awm/rvfs-testbed/experiments/seven_segment/seven_segment.kicad_pcb

## KiCad design Diagramas_y_Bocetos/Diagrama_kicad/Cascarrabias_Kicad/Cascarrabias_Kicad.kicad_sch

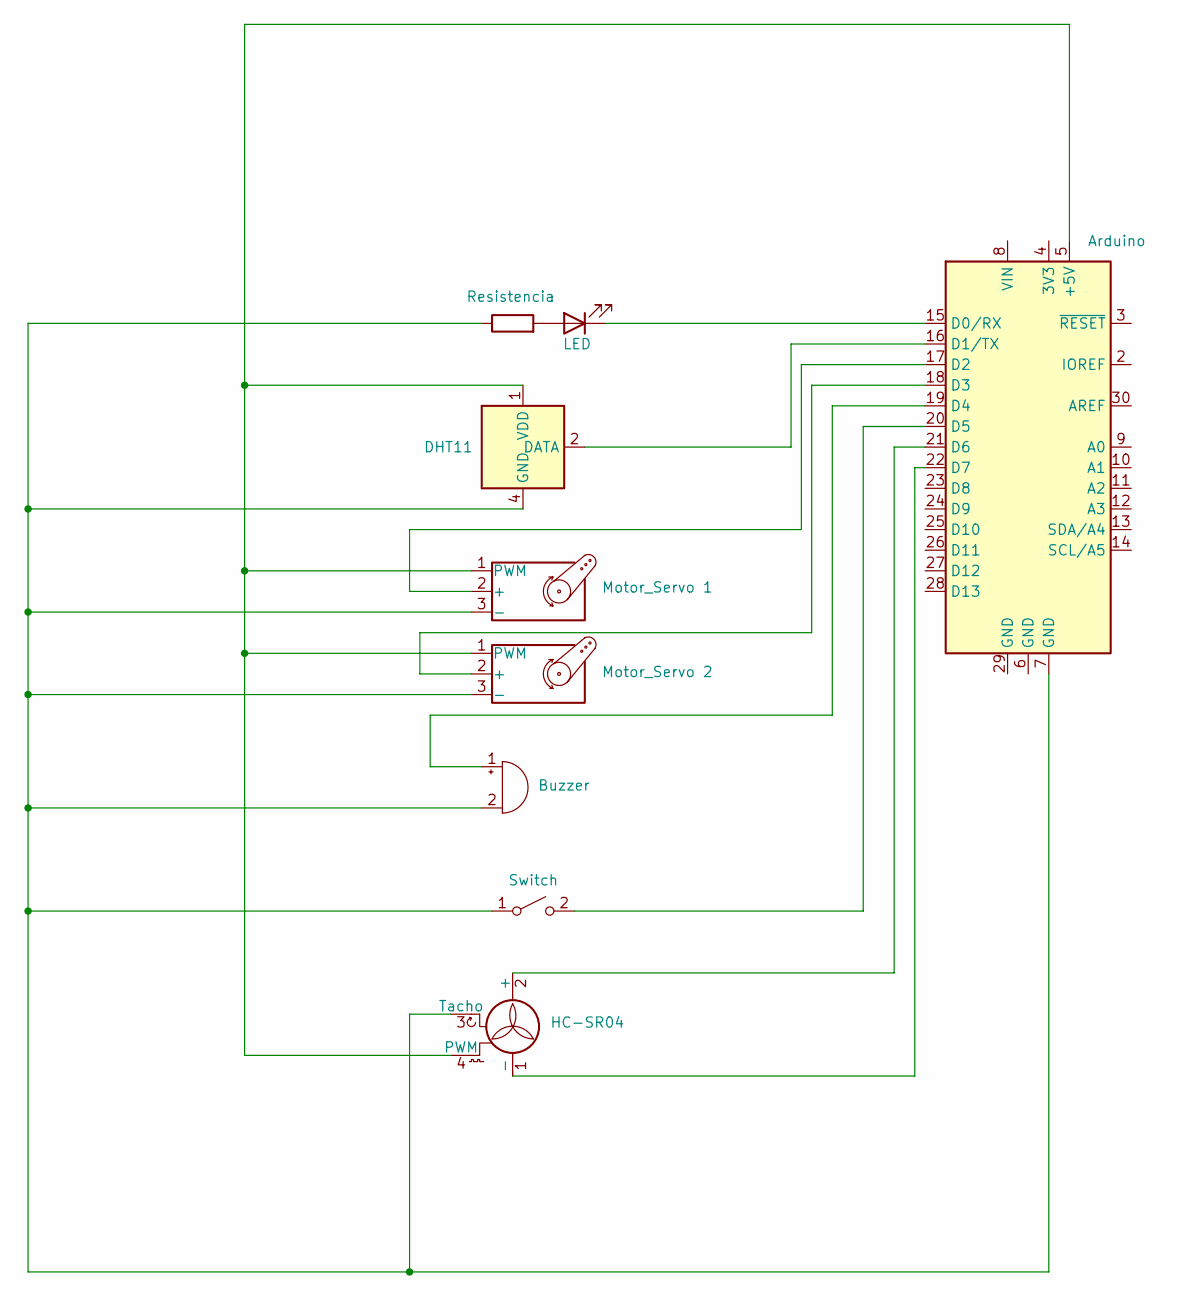
[picture p1: schematic Cascarrabias_Kicad.kicad_sch]

Parts:
A1: Arduino; Arduino_UNO_R2
BZ1: Buzzer
D1: LED
M1: Motor_Servo 1
M2: Motor_Servo 2
M3: HC-SR04
Resistencia: R
SW1: Switch
U1: DHT11; Aosong_DHT11_5.5x12.0_P2.54mm

Connections:
unnamed: A1.5 (+5V), M1.1 (PWM), M2.1 (PWM), M3.4 (PWM), U1.1 (VDD)
unnamed: A1.7 (GND), BZ1.2 (-), M1.3 (-), M2.3 (-), M3.3 (Tacho), Resistencia.1, SW1.1 (A), U1.4 (GND)
unnamed: A1.15 (D0/RX), D1.1 (K)
unnamed: A1.16 (D1/TX), U1.2 (DATA)
unnamed: A1.17 (D2), M1.2 (+)
unnamed: A1.18 (D3), M2.2 (+)
unnamed: A1.19 (D4), BZ1.1 (+)
unnamed: A1.20 (D5), SW1.2 (B)
unnamed: A1.21 (D6), M3.2 (+)
unnamed: A1.22 (D7), M3.1 (-)
unnamed: D1.2 (A), Resistencia.2
